TrojanPinata/tiny-keeb/caps/cap ref/1u.step

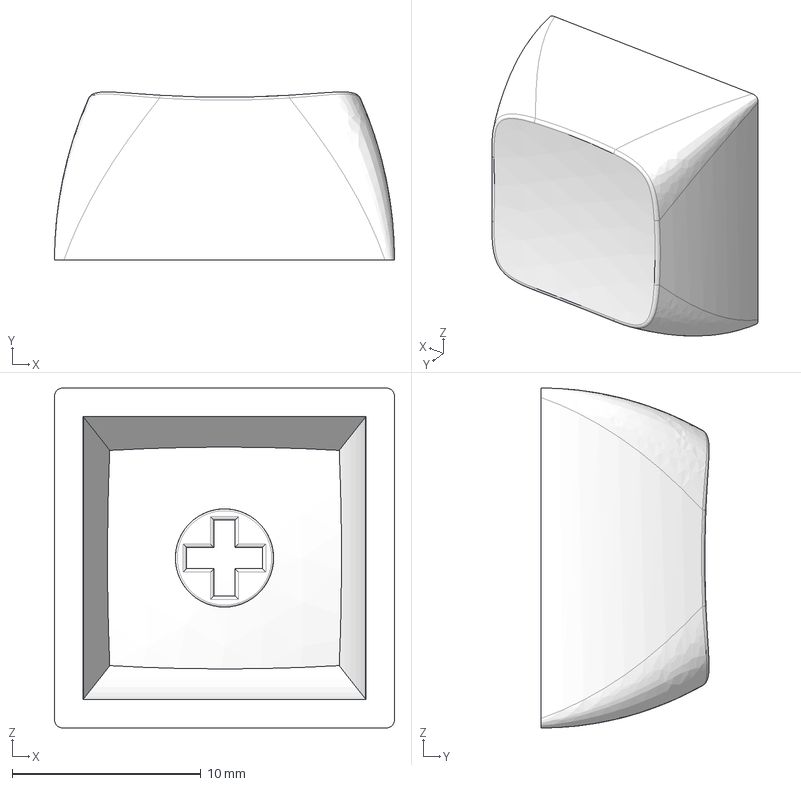
[picture p19: CAD file, 2024-11-29]
caps/cap ref/1u.step
18.0 x 8.90 x 18.0 mm
